gcastle2007/Voron-V2.2826/input_shaper/resonances_belts_test.png

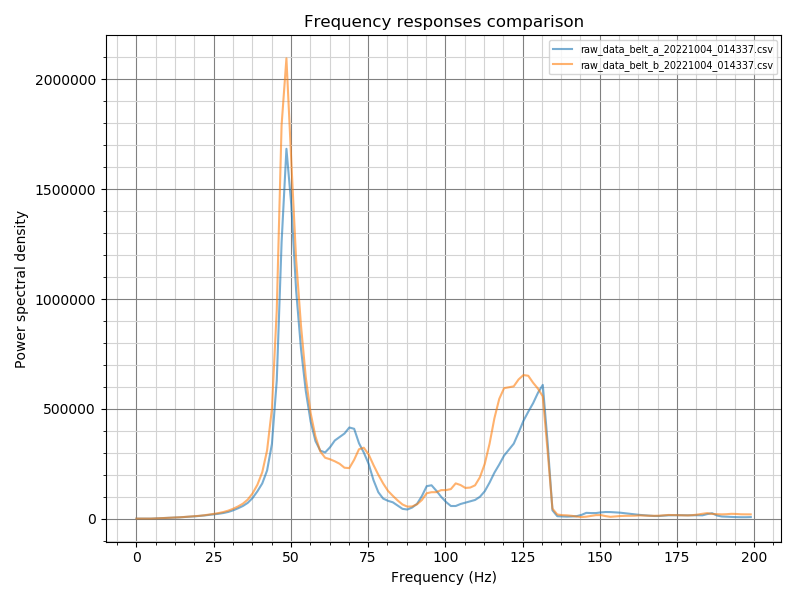
input_shaper/resonances_belts_test.png
