gcastle2007/Voron-V2.2826/original_backup/printer.cfg

[mcu]
serial: /dev/serial/by-id/<your-mcu-id>

[virtual_sdcard]
path: /home/pi/printer_data/gcodes
on_error_gcode: CANCEL_PRINT

[printer]
kinematics: none
max_velocity: 1000
max_accel: 1000
