gcastle2007/Voron-V2.2826/fans.cfg

#[temperature_fan RPI_external]
#sensor_type: temperature_host
#pin: PD14
#kick_start_time: 0.5
##target_temp: 51.0
#target_temp: 53.0
#min_temp: 5
#max_temp: 100
#control: watermark
#max_speed: 1

;[temperature_fan Raspberry_PI]
[controller_fan Raspberry-PI]
;sensor_type: temperature_host
pin: PD15
kick_start_time: 0.5
#target_temp: 51.0
;target_temp: 50.0
;min_temp: 5
;max_temp: 100
;control: watermark
#min_speed: 0.2
;max_speed: 0.5
fan_speed: 0.7

# MCU_FAN_1
[controller_fan FAN_MCU]
;[fan_generic Driver_fan]
pin: PD13
#fan_speed: 0.7
fan_speed: 1
kick_start_time: 0.5
;max_power: 0.3
idle_timeout: 900
#   The amount of time (in seconds) after a stepper driver or heater
#   was active and the fan should be kept running. The default
#   is 30 seconds.
idle_speed: 0.7
#   The fan speed (expressed as a value from 0.0 to 1.0) that the fan
#   will be set to when a heater or stepper driver was active and
#   before the idle_timeout is reached. The default is fan_speed.

[controller_fan FAN_RPI]
;[fan_generic Driver_fan]
pin: PD14
#fan_speed: 0.7
fan_speed: 1
kick_start_time: 0.5
;max_power: 0.3
idle_timeout: 900
#   The amount of time (in seconds) after a stepper driver or heater
#   was active and the fan should be kept running. The default
#   is 30 seconds.
idle_speed: 0.7
#   The fan speed (expressed as a value from 0.0 to 1.0) that the fan
#   will be set to when a heater or stepper driver was active and
#   before the idle_timeout is reached. The default is fan_speed.

[heater_fan hotend_fan]
pin: PE5
max_power: 1
fan_speed: 1
#kick_start_time: 0.5
heater: extruder
heater_temp: 50.0
shutdown_speed = 1

[fan]
##	Print Cooling Fan - FAN1 Connector
#pin: PA8
pin: PA3
max_power: 1.0
kick_start_time: 0.5
##	Depending on your fan, you may need to increase this value
##	if your fan will not start. Can change cycle_time (increase)
##	if your fan is not able to slow down effectively
#off_below: 0.10
off_below: 0.05
cycle_time: 0.008

#[fan_generic Vefash]
#pin: PD12
#kick_start_time: 0.5
#max_power: 1.0

[temperature_fan Vefach-Chamber]
pin: PD12
sensor_type: NTC 100K MGB18-104F39050L32
sensor_pin: PF4
kick_start_time: 0.5
target_temp: 50.0
min_temp: 5
max_temp: 100
control: watermark
max_speed: 1

# [fan_generic Nevermore]
# pin: PB11
# ;heater_temp: 50
# kick_start_time: 0.5
# max_power: 1.0
# ;idle_timeout: 300
# ;idle_speed: 1.0

[temperature_sensor Drivers]
sensor_type: NTC 100K MGB18-104F39050L32
sensor_pin: PF5

#[temperature_sensor chamber]
#sensor_type: NTC 100K MGB18-104F39050L32
#sensor_pin: PF4

[temperature_sensor BED_Ext]
sensor_type: NTC 100K MGB18-104F39050L32
sensor_pin: PF6
