gcastle2007/Voron-V2.2826/MACROS/g-codes.cfg

[gcode_macro M900]
gcode:
    {% set K = params.K|default(0) %}
    SET_PRESSURE_ADVANCE ADVANCE={K}

[gcode_macro M207]
gcode:
    {% set S = params.S|default(0) %}
    {% set F = params.F|default(0) %}
    SET_RETRACTION RETRACT_LENGTH={S} RETRACT_SPEED={F}
