gcastle2007/Voron-V2.2826/MACROS/low_temp_check.cfg

[gcode_macro LOW_TEMP_CHECK]
gcode:
    {% set extruder_temp = params.T|default(210)|float %}
    {% if printer.extruder.target > extruder_temp %}                            # if there is a setpoint for extruder
        {% set extruder_temp = printer.extruder.target %}
    {% endif %}
    {% if printer.extruder.temperature < extruder_temp %}                       # heat to the target
        M117 Heating to {extruder_temp}
        SET_HEATER_TEMPERATURE HEATER=extruder TARGET={extruder_temp}
        TEMPERATURE_WAIT SENSOR=extruder MINIMUM={extruder_temp}
    {% endif %}
