gcastle2007/Voron-V2.2826/thermistor_ATC-Semitec-104GT-2.cfg

[extruder]
sensor_type: ATC Semitec 104GT-2
#   One of "EPCOS 100K B57560G104F", "ATC Semitec 104GT-2",
#   "ATC Semitec 104NT-4-R025H42G", "Generic 3950",
#   "Honeywell 100K 135-104LAG-J01", "NTC 100K MGB18-104F39050L32",
#   "SliceEngineering 450", or "TDK NTCG104LH104JT1"
sensor_pin: PF7
#   Analog input pin connected to the thermistor. This parameter must
#   be provided.
#pullup_resistor: 4700
#   The resistance (in ohms) of the pullup attached to the thermistor.
#   The default is 4700 ohms.
#inline_resistor: 0
#   The resistance (in ohms) of an extra (not heat varying) resistor
#   that is placed inline with the thermistor. It is rare to set this.
#   The default is 0 ohms.
